alighieribot/lpc11u14-board-bringup/KiCad/Projeto_Final/Footprints/70246-1002/70246-1002.stp

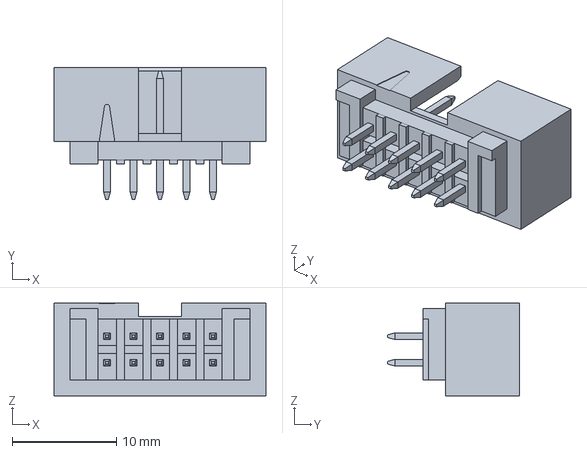
[picture p62: CAD file, 2026-09-02]
KiCad/Projeto_Final/Footprints/70246-1002/70246-1002.stp
20.3 x 12.7 x 8.89 mm
