alighieribot/lpc11u14-board-bringup/Código/PBLE02/src/hardware/LED.h

/*
 *  Created on: 5 de jul. de 2025
 *      Author: Osmar Bruno
 */

#ifndef LED_H
#define LED_H
	#include "../programa.h"
    void iniciaLED(void);
    void ligaLED(int);
    void desligaLED(int);
    void defineLED(int, int);
    void toggleLED(int);
#endif
