alighieribot/lpc11u14-board-bringup/Código/PBLE02/src/util.h

/*
 *  Created on: 5 de jul. de 2025
 *      Author: Osmar Bruno
 */

#ifndef UTIL_H
#define UTIL_H
	#define GANHO_AMPOP 0.605
	float manual_fabs(float);
	long manual_roundf(float);
	char* floatParaString(float, char*);
#endif
